AKAMEDIASYSTEM/aka-multispec-jar/network.ino

void initAPIPConfigStruct(WiFi_AP_IPConfig &in_WM_AP_IPconfig)
{
  in_WM_AP_IPconfig._ap_static_ip   = APStaticIP;
  in_WM_AP_IPconfig._ap_static_gw   = APStaticGW;
  in_WM_AP_IPconfig._ap_static_sn   = APStaticSN;
}

void initSTAIPConfigStruct(WiFi_STA_IPConfig &in_WM_STA_IPconfig)
{
  in_WM_STA_IPconfig._sta_static_ip   = stationIP;
  in_WM_STA_IPconfig._sta_static_gw   = gatewayIP;
  in_WM_STA_IPconfig._sta_static_sn   = netMask;
#if USE_CONFIGURABLE_DNS
  in_WM_STA_IPconfig._sta_static_dns1 = dns1IP;
  in_WM_STA_IPconfig._sta_static_dns2 = dns2IP;
#endif
}

void displayIPConfigStruct(WiFi_STA_IPConfig in_WM_STA_IPconfig)
{
  LOGERROR3(F("stationIP ="), in_WM_STA_IPconfig._sta_static_ip, ", gatewayIP =", in_WM_STA_IPconfig._sta_static_gw);
  LOGERROR1(F("netMask ="), in_WM_STA_IPconfig._sta_static_sn);
#if USE_CONFIGURABLE_DNS
  LOGERROR3(F("dns1IP ="), in_WM_STA_IPconfig._sta_static_dns1, ", dns2IP =", in_WM_STA_IPconfig._sta_static_dns2);
#endif
}

void configWiFi(WiFi_STA_IPConfig in_WM_STA_IPconfig)
{
#if USE_CONFIGURABLE_DNS
  // Set static IP, Gateway, Subnetmask, DNS1 and DNS2. New in v1.0.5
  WiFi.config(in_WM_STA_IPconfig._sta_static_ip, in_WM_STA_IPconfig._sta_static_gw, in_WM_STA_IPconfig._sta_static_sn, in_WM_STA_IPconfig._sta_static_dns1, in_WM_STA_IPconfig._sta_static_dns2);
#else
  // Set static IP, Gateway, Subnetmask, Use auto DNS1 and DNS2.
  WiFi.config(in_WM_STA_IPconfig._sta_static_ip, in_WM_STA_IPconfig._sta_static_gw, in_WM_STA_IPconfig._sta_static_sn);
#endif
}


uint8_t connectMultiWiFi()
{
#if ESP32
  // For ESP32, this better be 0 to shorten the connect time.
  // For ESP32-S2, must be > 500
#if ( ARDUINO_ESP32S2_DEV || ARDUINO_FEATHERS2 || ARDUINO_PROS2 || ARDUINO_MICROS2 )
#define WIFI_MULTI_1ST_CONNECT_WAITING_MS           500L
#else
  // For ESP32 core v1.0.6, must be >= 500
#define WIFI_MULTI_1ST_CONNECT_WAITING_MS           800L
#endif
#else
  // For ESP8266, this better be 2200 to enable connect the 1st time
#define WIFI_MULTI_1ST_CONNECT_WAITING_MS             2200L
#endif

#define WIFI_MULTI_CONNECT_WAITING_MS                   100L

  uint8_t status;

  LOGERROR(F("ConnectMultiWiFi with :"));

  if ( (Router_SSID != "") && (Router_Pass != "") )
  {
    LOGERROR3(F("* Flash-stored Router_SSID = "), Router_SSID, F(", Router_Pass = "), Router_Pass );
  }

  for (uint8_t i = 0; i < NUM_WIFI_CREDENTIALS; i++)
  {
    // Don't permit NULL SSID and password len < MIN_AP_PASSWORD_SIZE (8)
    if ( (String(WM_config.WiFi_Creds[i].wifi_ssid) != "") && (strlen(WM_config.WiFi_Creds[i].wifi_pw) >= MIN_AP_PASSWORD_SIZE) )
    {
      LOGERROR3(F("* Additional SSID = "), WM_config.WiFi_Creds[i].wifi_ssid, F(", PW = "), WM_config.WiFi_Creds[i].wifi_pw );
    }
  }

  LOGERROR(F("Connecting MultiWifi..."));

  WiFi.mode(WIFI_STA);

#if !USE_DHCP_IP
  // New in v1.4.0
  configWiFi(WM_STA_IPconfig);
  //////
#endif

  int i = 0;
  status = wifiMulti.run();
  delay(WIFI_MULTI_1ST_CONNECT_WAITING_MS);

  while ( ( i++ < 20 ) && ( status != WL_CONNECTED ) )
  {
    status = wifiMulti.run();

    if ( status == WL_CONNECTED )
      break;
    else
      delay(WIFI_MULTI_CONNECT_WAITING_MS);
  }

  if ( status == WL_CONNECTED )
  {
    LOGERROR1(F("WiFi connected after time: "), i);
    LOGERROR3(F("SSID:"), WiFi.SSID(), F(",RSSI="), WiFi.RSSI());
    LOGERROR3(F("Channel:"), WiFi.channel(), F(",IP address:"), WiFi.localIP() );
  }
  else
    LOGERROR(F("WiFi not connected"));

  return status;
}

void toggleLED()
{
  //toggle state
  digitalWrite(LED_BUILTIN, !digitalRead(LED_BUILTIN));
}

void heartBeatPrint()
{
  static int num = 1;

  if (WiFi.status() == WL_CONNECTED)
    Serial.print(F("H "));        // H means connected to WiFi
  else
    Serial.print(F("F "));        // F means not connected to WiFi

  if (num == 80)
  {
    Serial.println();
    num = 1;
  }
  else if (num++ % 10 == 0)
  {
    Serial.print(F(" "));
  }
}

void check_WiFi()
{
  if ( (WiFi.status() != WL_CONNECTED) )
  {
    Serial.println(F("\nWiFi lost. Call connectMultiWiFi in loop"));
    connectMultiWiFi();
  }
}

void check_status()
{
  static ulong checkstatus_timeout  = 0;
  static ulong LEDstatus_timeout    = 0;
  static ulong checkwifi_timeout    = 0;

  static ulong current_millis;

#define WIFICHECK_INTERVAL    1000L
#define LED_INTERVAL          2000L
#define HEARTBEAT_INTERVAL    10000L

  current_millis = millis();

  // Check WiFi every WIFICHECK_INTERVAL (1) seconds.
  if ((current_millis > checkwifi_timeout) || (checkwifi_timeout == 0))
  {
    check_WiFi();
    checkwifi_timeout = current_millis + WIFICHECK_INTERVAL;
  }

  if ((current_millis > LEDstatus_timeout) || (LEDstatus_timeout == 0))
  {
    // Toggle LED at LED_INTERVAL = 2s
    toggleLED();
    LEDstatus_timeout = current_millis + LED_INTERVAL;
  }

  // Print hearbeat every HEARTBEAT_INTERVAL (10) seconds.
  if ((current_millis > checkstatus_timeout) || (checkstatus_timeout == 0))
  {
    heartBeatPrint();
    checkstatus_timeout = current_millis + HEARTBEAT_INTERVAL;
  }
}

bool loadConfigData()
{
  File file = FileFS.open(CONFIG_FILENAME, "r");
  LOGERROR(F("LoadWiFiCfgFile "));

  memset(&WM_config,       0, sizeof(WM_config));

  // New in v1.4.0
  memset(&WM_STA_IPconfig, 0, sizeof(WM_STA_IPconfig));
  //////

  if (file)
  {
    file.readBytes((char *) &WM_config,   sizeof(WM_config));

    // New in v1.4.0
    file.readBytes((char *) &WM_STA_IPconfig, sizeof(WM_STA_IPconfig));
    //////

    file.close();
    LOGERROR(F("OK"));

    // New in v1.4.0
    displayIPConfigStruct(WM_STA_IPconfig);
    //////

    return true;
  }
  else
  {
    LOGERROR(F("failed"));

    return false;
  }
}

void saveConfigData()
{
  File file = FileFS.open(CONFIG_FILENAME, "w");
  LOGERROR(F("SaveWiFiCfgFile "));

  if (file)
  {
    file.write((uint8_t*) &WM_config,   sizeof(WM_config));

    displayIPConfigStruct(WM_STA_IPconfig);

    // New in v1.4.0
    file.write((uint8_t*) &WM_STA_IPconfig, sizeof(WM_STA_IPconfig));
    //////

    file.close();
    LOGERROR(F("OK"));
  }
  else
  {
    LOGERROR(F("failed"));
  }
}

void connectToMqtt() {
  Serial.println("Connecting to MQTT...");
  mqttClient.connect();
}

void onMqttConnect(bool sessionPresent) {
  Serial.println("Connected to MQTT.");
  Serial.print("Session present: ");
  Serial.println(sessionPresent);
}

void onMqttDisconnect(AsyncMqttClientDisconnectReason reason) {
  Serial.println("Disconnected from MQTT. ");
}

void onMqttPublish(uint16_t packetId) {
  Serial.print("Publish acknowledged.");
  Serial.print("  packetId: ");
  Serial.println(packetId);
}

void publishMQTT() {
  connectToMqtt();
  JSONVar payload;
  payload["distance"] =  series1[0];
  payload["co2"] =  series2[0];
  payload["tmp"] =  series3[0];
  payload["rh"] = series4[0];
  String jsonString = JSON.stringify(payload);
  uint16_t packetIdPub1 = mqttClient.publish(topicString.c_str(), 1, true, jsonString.c_str());
  if (DEBUG) {
    Serial.print("publish result is ");
    Serial.println(topicString);
    Serial.println(packetIdPub1);
    Serial.println(jsonString);
  }
}
